emaa877/Joystick-RF/img2.jpg

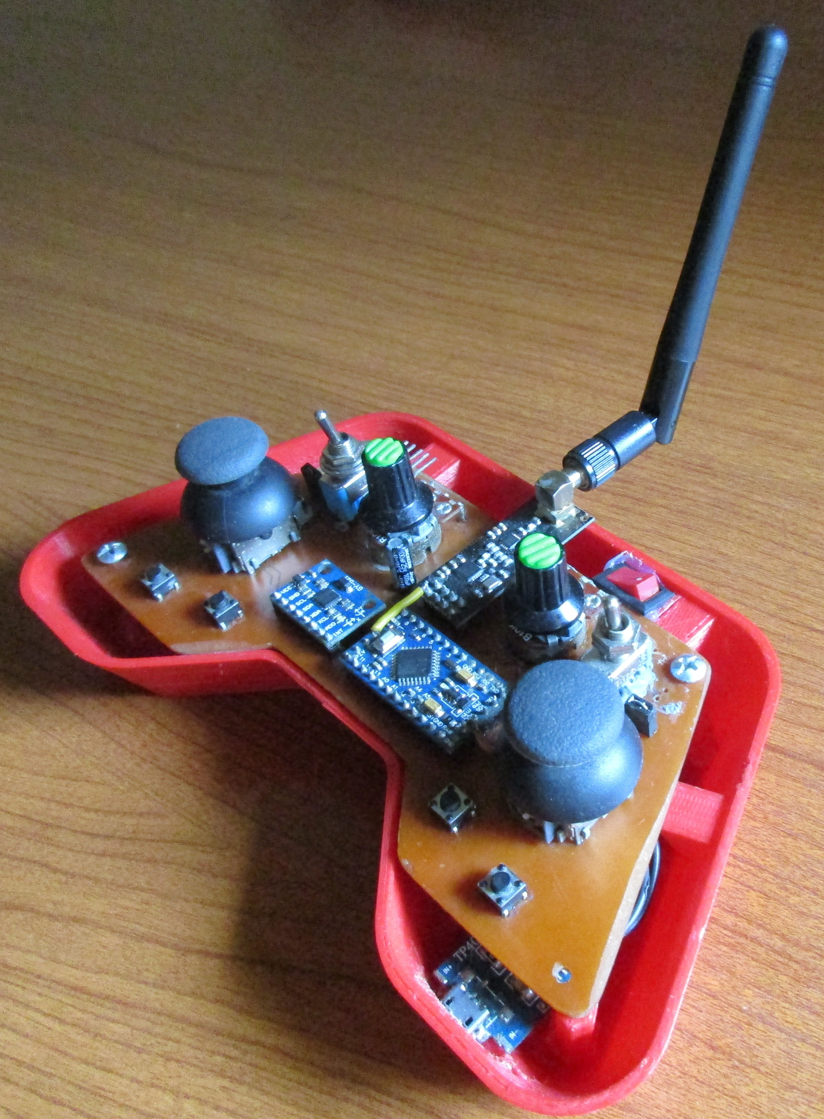
img2.jpg
