emaa877/Joystick-RF/img3.jpg

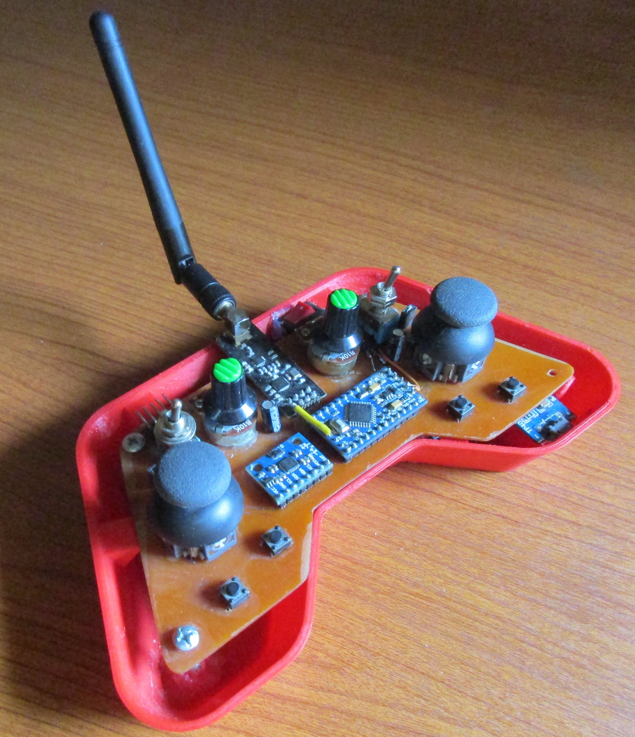
img3.jpg
