emaa877/Joystick-RF/joystick.png

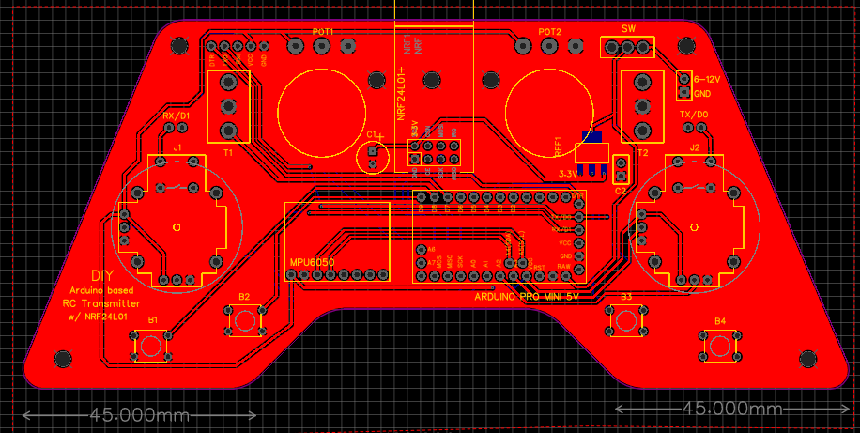
joystick.png
