emaa877/Joystick-RF/vJoySerialFeeder-1.5/Docs/images/ard0.png

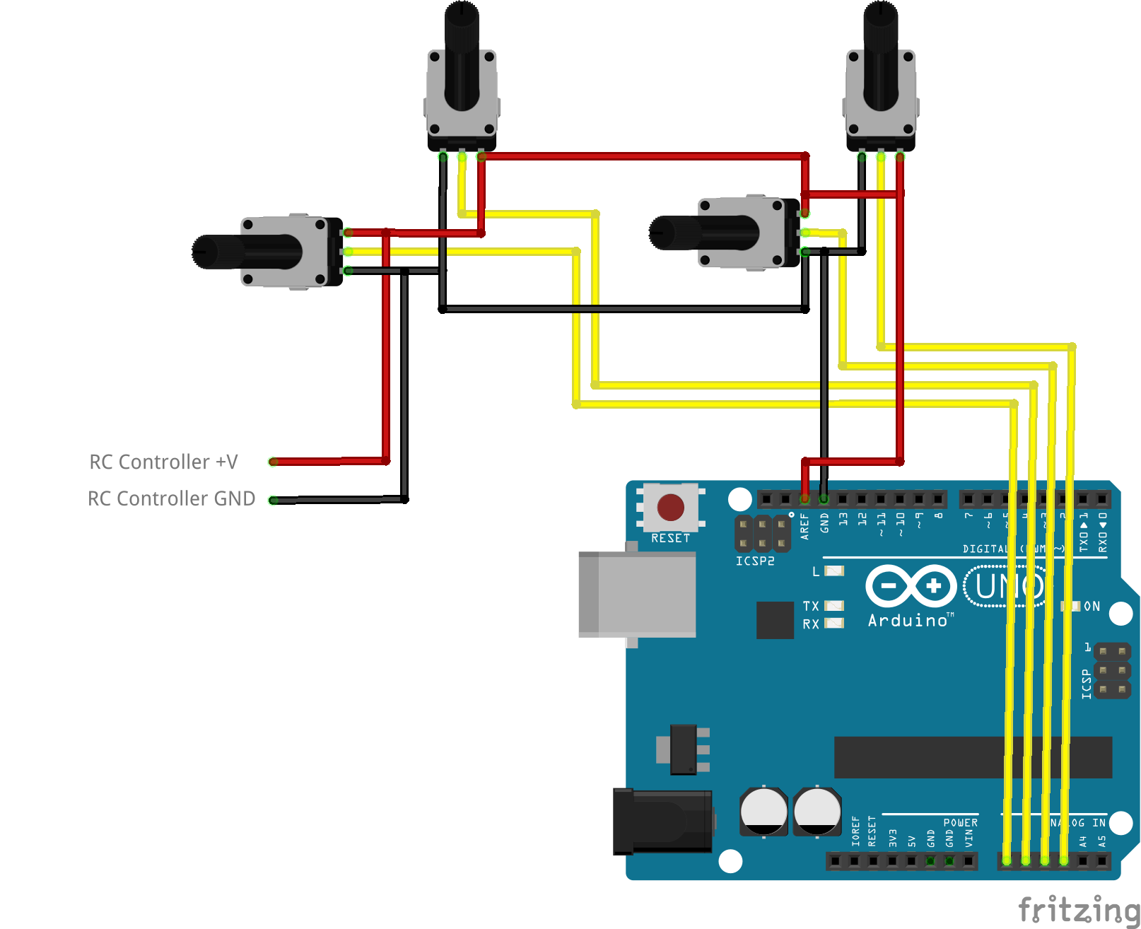
vJoySerialFeeder-1.5/Docs/images/ard0.png
