emaa877/Joystick-RF/vJoySerialFeeder-1.5/Docs/images/ard4.jpg

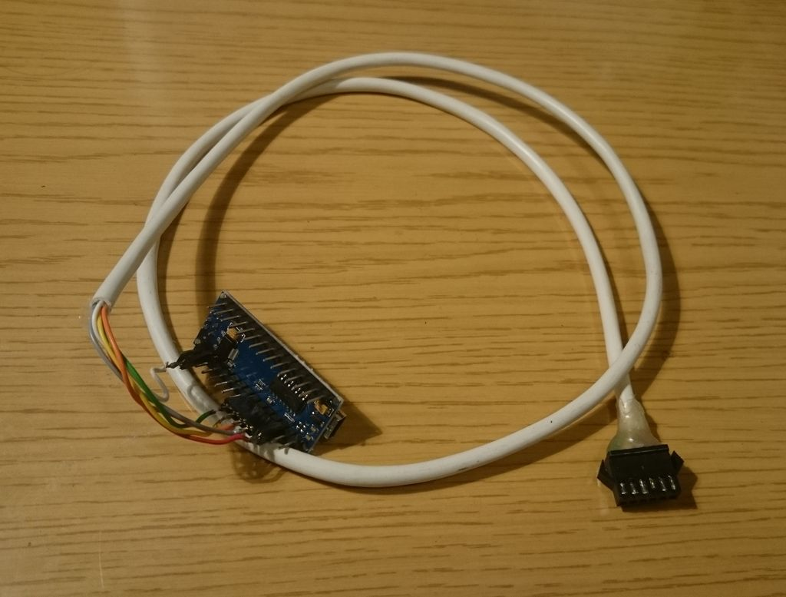
vJoySerialFeeder-1.5/Docs/images/ard4.jpg
