emaa877/Joystick-RF/vJoySerialFeeder-1.5/Docs/images/main-loop.png

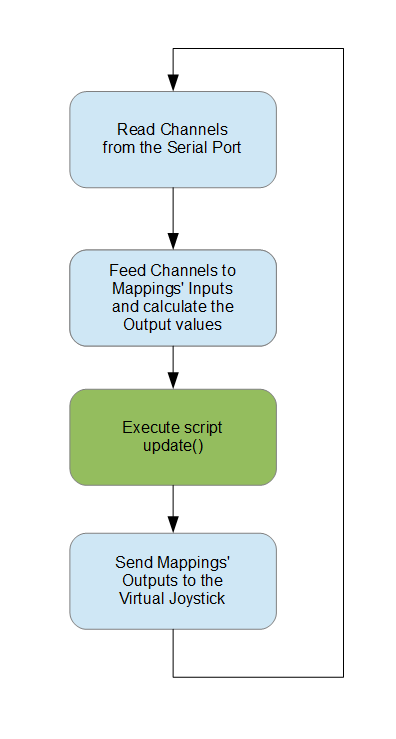
vJoySerialFeeder-1.5/Docs/images/main-loop.png
