emaa877/Joystick-RF/vJoySerialFeeder-1.5/Docs/images/axis-setup.png

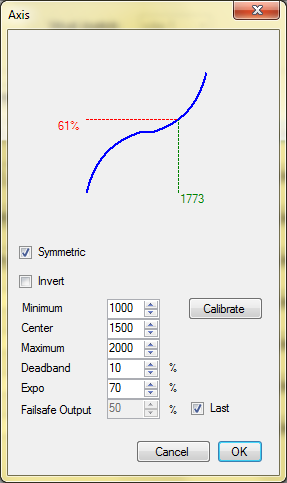
vJoySerialFeeder-1.5/Docs/images/axis-setup.png
