emaa877/Joystick-RF/vJoySerialFeeder-1.5/Docs/images/bitmap-setup.png

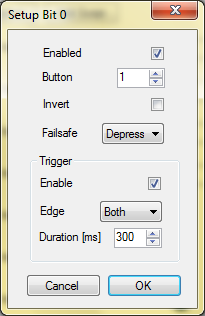
vJoySerialFeeder-1.5/Docs/images/bitmap-setup.png
