emaa877/Joystick-RF/vJoySerialFeeder-1.5/Docs/images/button-setup.png

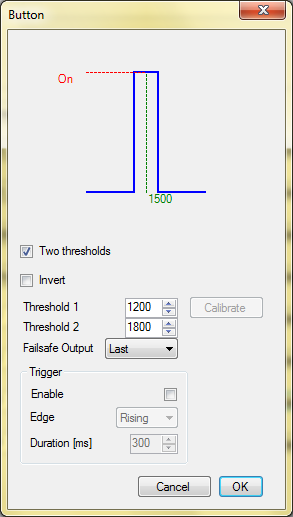
vJoySerialFeeder-1.5/Docs/images/button-setup.png
